S-March/realPlantNursery_Public/Firmware/sdCardFiles/webPage/projects/settingsPage/mediaAssets/imageAssets/background.jpg

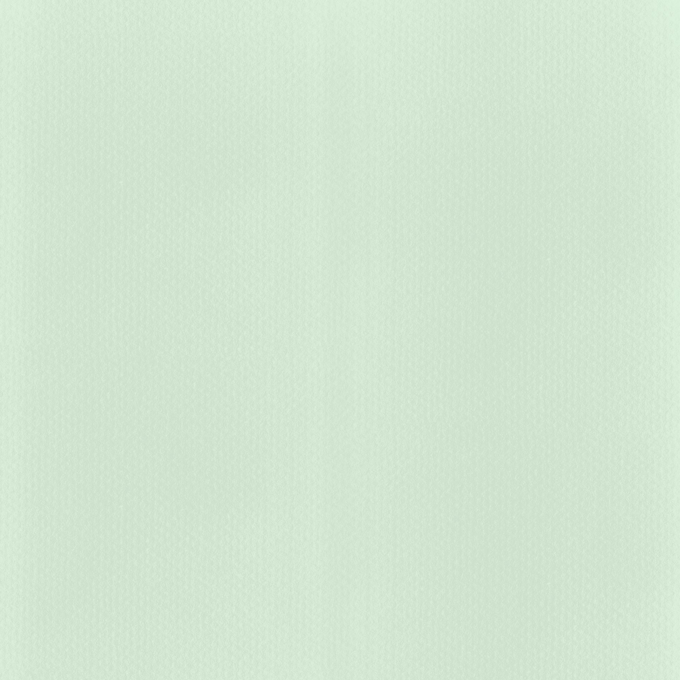
Firmware/sdCardFiles/webPage/projects/settingsPage/mediaAssets/imageAssets/background.jpg
