S-March/realPlantNursery_Public/Firmware/sdCardFiles/webPage/projects/settingsPage/mediaAssets/imageAssets/main.jpg

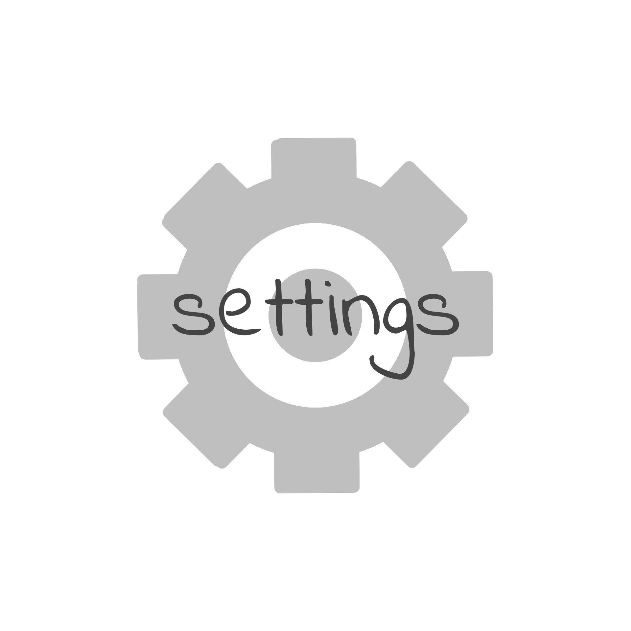
Firmware/sdCardFiles/webPage/projects/settingsPage/mediaAssets/imageAssets/main.jpg
