S-March/realPlantNursery_Public/Hardware/realPlantNursery/FabFiles/boardNumberOfParts.jpg

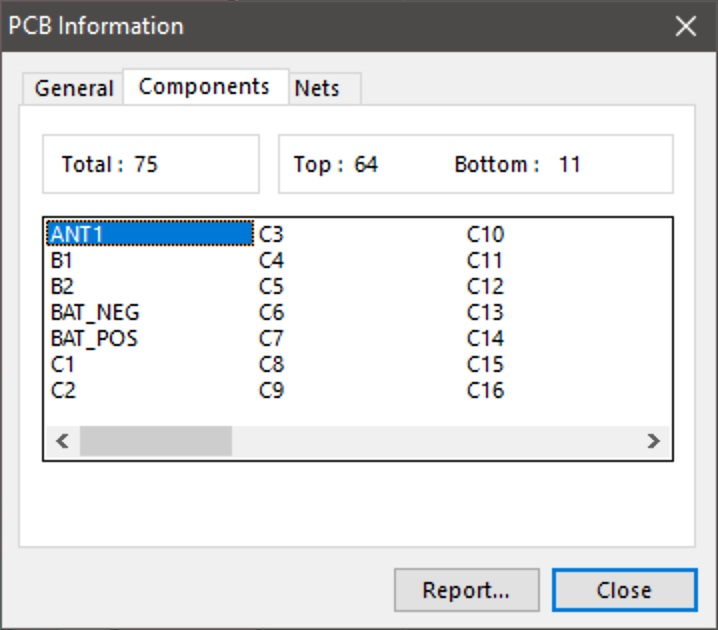
Hardware/realPlantNursery/FabFiles/boardNumberOfParts.jpg
