S-March/realPlantNursery_Public/Firmware/sdCardFiles/webPage/projects/mainPage/mediaAssets/imageAssets/instructionsBackground.gif

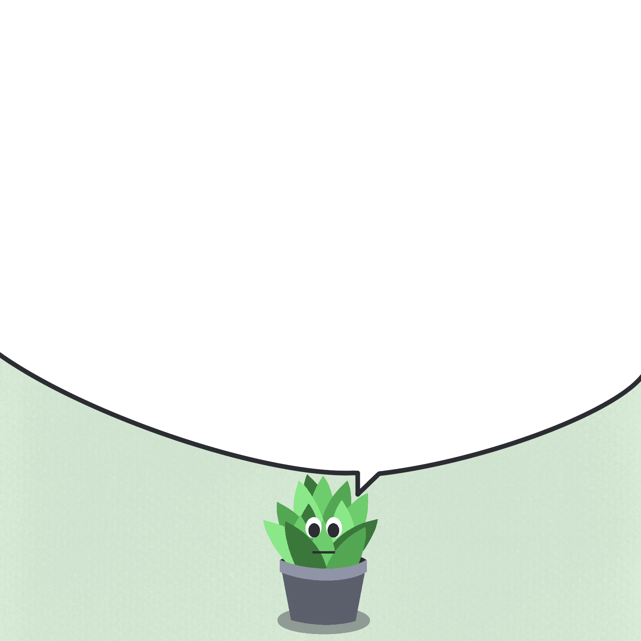
Firmware/sdCardFiles/webPage/projects/mainPage/mediaAssets/imageAssets/instructionsBackground.gif
